TunaHero/TheFin/Files/STLs/Tertiary Color/Short Plunger Cup.STL

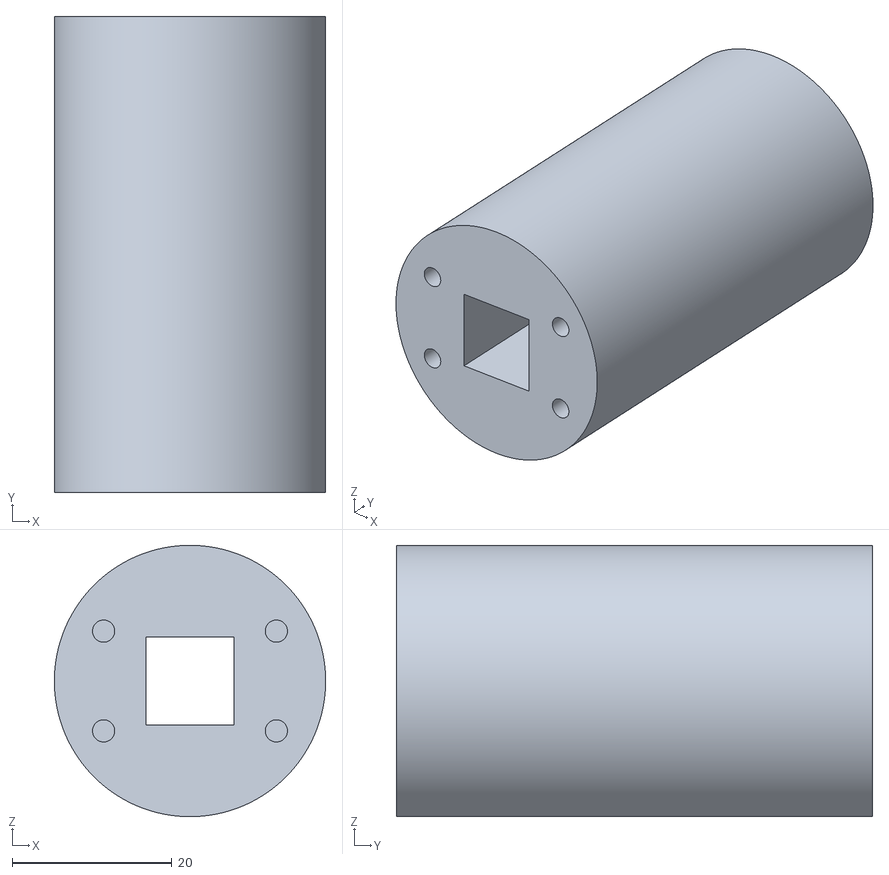
[picture p31: CAD file, 2022-12-15]
Files/STLs/Tertiary Color/Short Plunger Cup.STL
34.0 x 59.7 x 34.0
