TunaHero/TheFin/Files/STLs/Secondary Color/Logo Spacer.STL

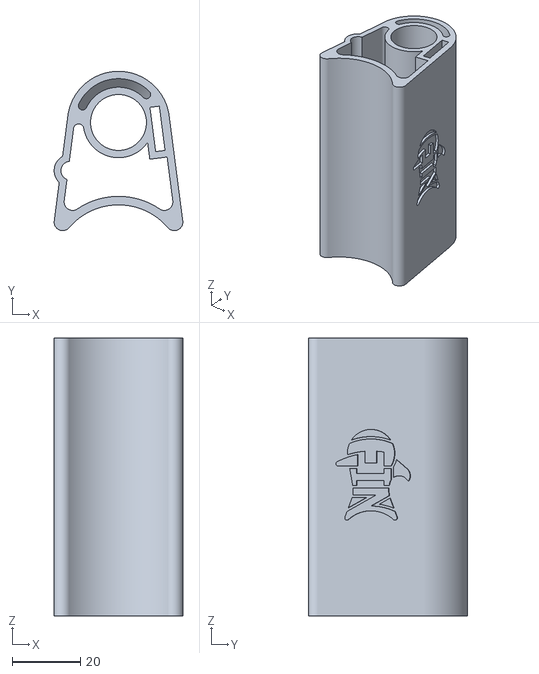
[picture p32: CAD file, 2023-02-03]
Files/STLs/Secondary Color/Logo Spacer.STL
37.8 x 46.8 x 81.6
