TunaHero/TheFin/Files/STLs/Tertiary Color/Plunger Catch Spacer.STL

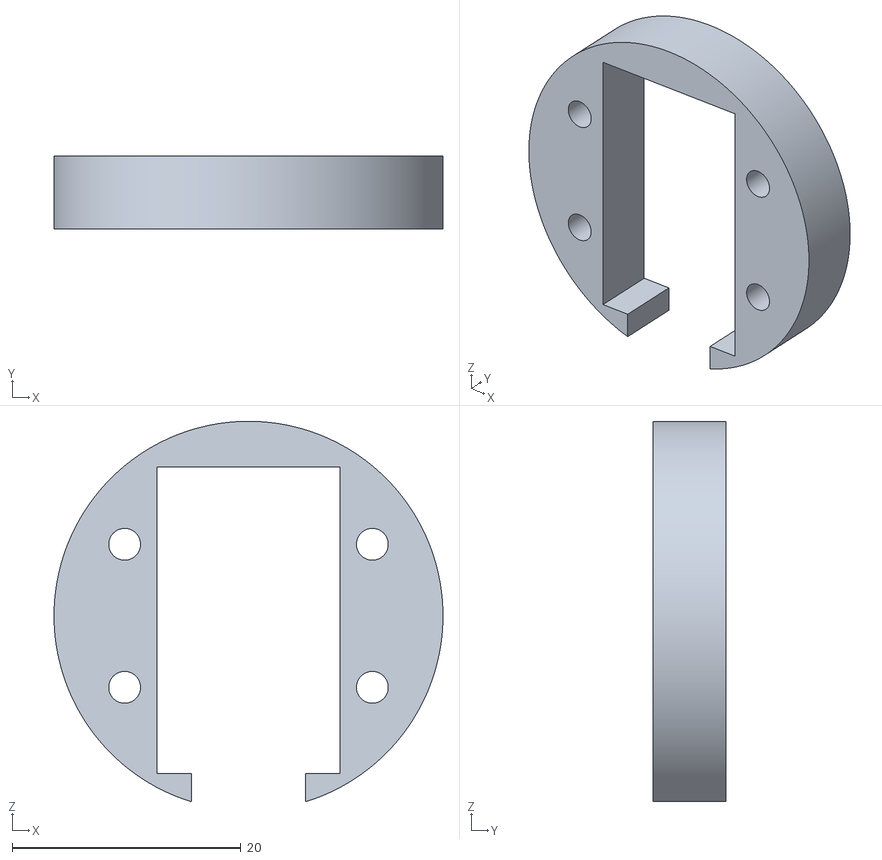
[picture p33: CAD file, 2022-12-15]
Files/STLs/Tertiary Color/Plunger Catch Spacer.STL
34.0 x 6.40 x 33.2
