TunaHero/TheFin/Files/STLs/Tertiary Color/Plunger Cap.STL

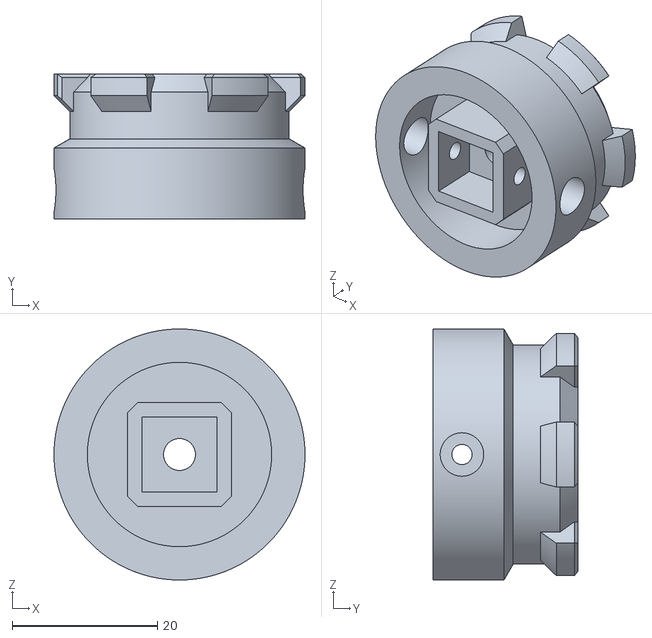
[picture p34: CAD file, 2022-12-15]
Files/STLs/Tertiary Color/Plunger Cap.STL
34.6 x 20.0 x 34.6
