TunaHero/TheFin/Files/STLs/Tertiary Color/Plunger Catch Cylinder.STL

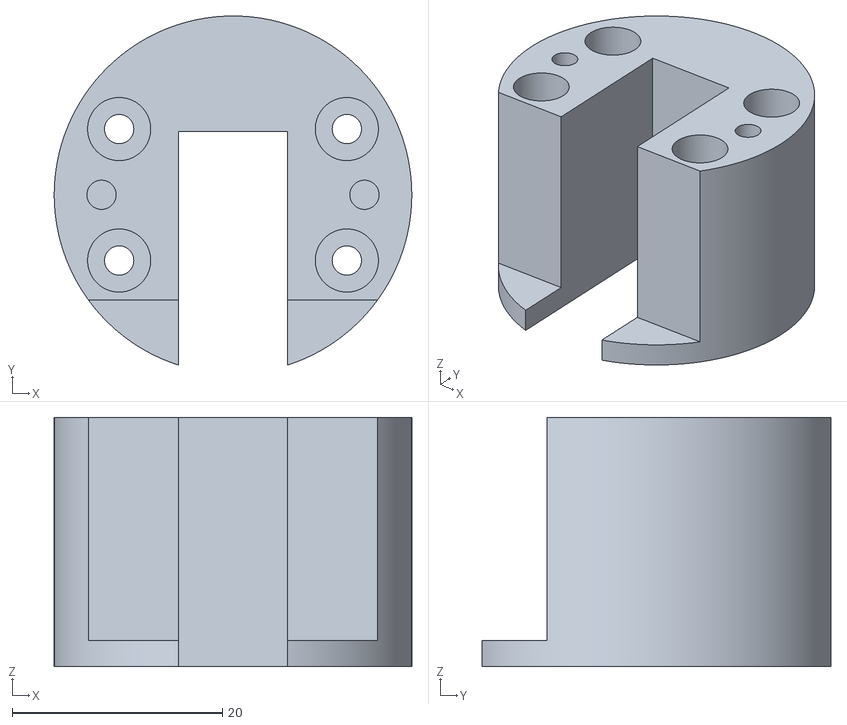
[picture p35: CAD file, 2022-12-15]
Files/STLs/Tertiary Color/Plunger Catch Cylinder.STL
34.0 x 33.2 x 23.7
